artemchip/PCBProduction/Galvo/NewMixer.jpg

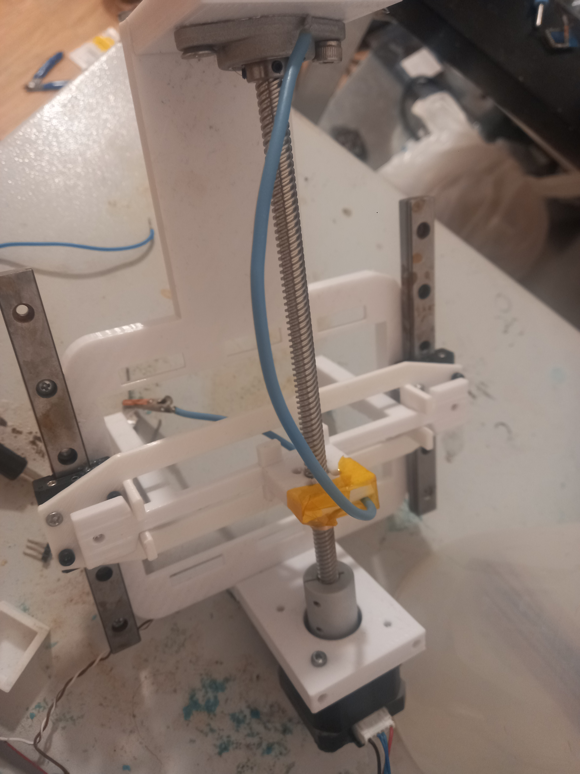
Galvo/NewMixer.jpg
